zaxioms0/CrossBox/esp32/src/globals.h

#include <Adafruit_Thermal.h>
#include <Arduino.h>
#include <Preferences.h>
#include <WiFi.h>
#include <WiFiManager.h>

#pragma once
#define RX 25          // YELLOW
#define TX 26          // WHITE
#define BUTT 19        // FRONT WIRE
#define BUTT_LED_OUT 5 // RIGHT WIRE
#define BUTT_LED 18    // LEFT WIRE
#define ONBOARD_LED 2
#define ALI_EXPRESS 1

enum CrossType { NYT, Puzzmo };

extern WiFiManager wm;
extern WiFiManagerParameter print_time_param;
extern WiFiManagerParameter nyts_param;
extern WiFiManagerParameter crosstype_param;

extern Preferences prefs;
extern Adafruit_Thermal printer;

extern const int MAX_BOARD;
extern const int SCRATCH_SIZE;
extern const int TEXT_WIDTH;
extern int board_px;
extern bool print_today;
extern int print_hr;
extern char nyts[];
extern char scratch[];
extern unsigned long press_time;
extern unsigned int ctr;
extern bool pressed;
extern char ssid[];
extern char wifi_pass[];
extern CrossType primary_cross;
